metaneutrons/Amiga1200-Plus/Firmware/Keyboard/KeyboardController/KeyboardController/src/driver_init.c

/**
 * \file
 *
 * \brief Driver initialization.
 *
 (c) 2018 Microchip Technology Inc. and its subsidiaries.

    Subject to your compliance with these terms,you may use this software and
    any derivatives exclusively with Microchip products.It is your responsibility
    to comply with third party license terms applicable to your use of third party
    software (including open source software) that may accompany Microchip software.

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
    IN NO EVENT WILL MICROCHIP BE LIABLE FOR ANY INDIRECT, SPECIAL, PUNITIVE,
    INCIDENTAL OR CONSEQUENTIAL LOSS, DAMAGE, COST OR EXPENSE OF ANY KIND
    WHATSOEVER RELATED TO THE SOFTWARE, HOWEVER CAUSED, EVEN IF MICROCHIP HAS
    BEEN ADVISED OF THE POSSIBILITY OR THE DAMAGES ARE FORESEEABLE. TO THE
    FULLEST EXTENT ALLOWED BY LAW, MICROCHIP'S TOTAL LIABILITY ON ALL CLAIMS IN
    ANY WAY RELATED TO THIS SOFTWARE WILL NOT EXCEED THE AMOUNT OF FEES, IF ANY,
    THAT YOU HAVE PAID DIRECTLY TO MICROCHIP FOR THIS SOFTWARE.
 *
 */

/*
 * Code generated by START.
 *
 * This file will be overwritten when reconfiguring your START project.
 * Please copy examples or other code you want to keep to a separate file
 * to avoid losing it when reconfiguring.
 */

#include "driver_init.h"
#include <system.h>

/**
 * \brief System initialization
 */
void system_init()
{
	mcu_init();

	/* PORT setting on PA0 */

	// Set pin direction to input
	Y8_set_dir(PORT_DIR_IN);

	Y8_set_pull_mode(
	    // <y> Pull configuration
	    // <id> pad_pull_config
	    // <PORT_PULL_OFF"> Off
	    // <PORT_PULL_UP"> Pull-up
	    PORT_PULL_UP);

	/* PORT setting on PA1 */

	// Set pin direction to input
	Y9_set_dir(PORT_DIR_IN);

	Y9_set_pull_mode(
	    // <y> Pull configuration
	    // <id> pad_pull_config
	    // <PORT_PULL_OFF"> Off
	    // <PORT_PULL_UP"> Pull-up
	    PORT_PULL_UP);

	/* PORT setting on PA2 */

	// Set pin direction to input
	Y10_set_dir(PORT_DIR_IN);

	Y10_set_pull_mode(
	    // <y> Pull configuration
	    // <id> pad_pull_config
	    // <PORT_PULL_OFF"> Off
	    // <PORT_PULL_UP"> Pull-up
	    PORT_PULL_UP);

	/* PORT setting on PA3 */

	// Set pin direction to input
	Y11_set_dir(PORT_DIR_IN);

	Y11_set_pull_mode(
	    // <y> Pull configuration
	    // <id> pad_pull_config
	    // <PORT_PULL_OFF"> Off
	    // <PORT_PULL_UP"> Pull-up
	    PORT_PULL_UP);

	/* PORT setting on PA4 */

	// Set pin direction to input
	Y12_set_dir(PORT_DIR_IN);

	Y12_set_pull_mode(
	    // <y> Pull configuration
	    // <id> pad_pull_config
	    // <PORT_PULL_OFF"> Off
	    // <PORT_PULL_UP"> Pull-up
	    PORT_PULL_UP);

	/* PORT setting on PA5 */

	// Set pin direction to input
	Y13_set_dir(PORT_DIR_IN);

	Y13_set_pull_mode(
	    // <y> Pull configuration
	    // <id> pad_pull_config
	    // <PORT_PULL_OFF"> Off
	    // <PORT_PULL_UP"> Pull-up
	    PORT_PULL_UP);

	/* PORT setting on PA6 */

	// Set pin direction to input
	Y14_set_dir(PORT_DIR_IN);

	Y14_set_pull_mode(
	    // <y> Pull configuration
	    // <id> pad_pull_config
	    // <PORT_PULL_OFF"> Off
	    // <PORT_PULL_UP"> Pull-up
	    PORT_PULL_UP);

	/* PORT setting on PB0 */

	// Set pin direction to output
	X2_set_dir(PORT_DIR_OUT);

	X2_set_level(
	    // <y> Initial level
	    // <id> pad_initial_level
	    // <false"> Low
	    // <true"> High
	    false);

	/* PORT setting on PB1 */

	// Set pin direction to input
	RALT_set_dir(PORT_DIR_IN);

	RALT_set_pull_mode(
	    // <y> Pull configuration
	    // <id> pad_pull_config
	    // <PORT_PULL_OFF"> Off
	    // <PORT_PULL_UP"> Pull-up
	    PORT_PULL_UP);

	/* PORT setting on PB2 */

	// Set pin direction to input
	RAMI_set_dir(PORT_DIR_IN);

	RAMI_set_pull_mode(
	    // <y> Pull configuration
	    // <id> pad_pull_config
	    // <PORT_PULL_OFF"> Off
	    // <PORT_PULL_UP"> Pull-up
	    PORT_PULL_UP);

	/* PORT setting on PB3 */

	// Set pin direction to input
	CTRL_set_dir(PORT_DIR_IN);

	CTRL_set_pull_mode(
	    // <y> Pull configuration
	    // <id> pad_pull_config
	    // <PORT_PULL_OFF"> Off
	    // <PORT_PULL_UP"> Pull-up
	    PORT_PULL_UP);

	/* PORT setting on PB4 */

	// Set pin direction to input
	LSHF_set_dir(PORT_DIR_IN);

	LSHF_set_pull_mode(
	    // <y> Pull configuration
	    // <id> pad_pull_config
	    // <PORT_PULL_OFF"> Off
	    // <PORT_PULL_UP"> Pull-up
	    PORT_PULL_UP);

	/* PORT setting on PB5 */

	// Set pin direction to input
	LALT_set_dir(PORT_DIR_IN);

	LALT_set_pull_mode(
	    // <y> Pull configuration
	    // <id> pad_pull_config
	    // <PORT_PULL_OFF"> Off
	    // <PORT_PULL_UP"> Pull-up
	    PORT_PULL_UP);

	/* PORT setting on PB6 */

	// Set pin direction to input
	LAMI_set_dir(PORT_DIR_IN);

	LAMI_set_pull_mode(
	    // <y> Pull configuration
	    // <id> pad_pull_config
	    // <PORT_PULL_OFF"> Off
	    // <PORT_PULL_UP"> Pull-up
	    PORT_PULL_UP);

	/* PORT setting on PB7 */

	// Set pin direction to output
	CapsLockLed_set_dir(PORT_DIR_OUT);

	CapsLockLed_set_level(
	    // <y> Initial level
	    // <id> pad_initial_level
	    // <false"> Low
	    // <true"> High
	    false);

	/* PORT setting on PC0 */

	// Set pin direction to input
	Y0_set_dir(PORT_DIR_IN);

	Y0_set_pull_mode(
	    // <y> Pull configuration
	    // <id> pad_pull_config
	    // <PORT_PULL_OFF"> Off
	    // <PORT_PULL_UP"> Pull-up
	    PORT_PULL_UP);

	/* PORT setting on PC1 */

	// Set pin direction to input
	Y1_set_dir(PORT_DIR_IN);

	Y1_set_pull_mode(
	    // <y> Pull configuration
	    // <id> pad_pull_config
	    // <PORT_PULL_OFF"> Off
	    // <PORT_PULL_UP"> Pull-up
	    PORT_PULL_UP);

	/* PORT setting on PC2 */

	// Set pin direction to input
	Y2_set_dir(PORT_DIR_IN);

	Y2_set_pull_mode(
	    // <y> Pull configuration
	    // <id> pad_pull_config
	    // <PORT_PULL_OFF"> Off
	    // <PORT_PULL_UP"> Pull-up
	    PORT_PULL_UP);

	/* PORT setting on PC3 */

	// Set pin direction to input
	Y3_set_dir(PORT_DIR_IN);

	Y3_set_pull_mode(
	    // <y> Pull configuration
	    // <id> pad_pull_config
	    // <PORT_PULL_OFF"> Off
	    // <PORT_PULL_UP"> Pull-up
	    PORT_PULL_UP);

	/* PORT setting on PC4 */

	// Set pin direction to input
	Y4_set_dir(PORT_DIR_IN);

	Y4_set_pull_mode(
	    // <y> Pull configuration
	    // <id> pad_pull_config
	    // <PORT_PULL_OFF"> Off
	    // <PORT_PULL_UP"> Pull-up
	    PORT_PULL_UP);

	/* PORT setting on PC5 */

	// Set pin direction to input
	Y5_set_dir(PORT_DIR_IN);

	Y5_set_pull_mode(
	    // <y> Pull configuration
	    // <id> pad_pull_config
	    // <PORT_PULL_OFF"> Off
	    // <PORT_PULL_UP"> Pull-up
	    PORT_PULL_UP);

	/* PORT setting on PC6 */

	// Set pin direction to input
	Y6_set_dir(PORT_DIR_IN);

	Y6_set_pull_mode(
	    // <y> Pull configuration
	    // <id> pad_pull_config
	    // <PORT_PULL_OFF"> Off
	    // <PORT_PULL_UP"> Pull-up
	    PORT_PULL_UP);

	/* PORT setting on PC7 */

	// Set pin direction to input
	Y7_set_dir(PORT_DIR_IN);

	Y7_set_pull_mode(
	    // <y> Pull configuration
	    // <id> pad_pull_config
	    // <PORT_PULL_OFF"> Off
	    // <PORT_PULL_UP"> Pull-up
	    PORT_PULL_UP);

	/* PORT setting on PD0 */

	// Set pin direction to output
	KB_CLOCK_set_dir(PORT_DIR_OUT);

	KB_CLOCK_set_level(
	    // <y> Initial level
	    // <id> pad_initial_level
	    // <false"> Low
	    // <true"> High
	    false);

	/* PORT setting on PD1 */

	// Set pin direction to output
	KB_DATA_set_dir(PORT_DIR_OUT);

	KB_DATA_set_level(
	    // <y> Initial level
	    // <id> pad_initial_level
	    // <false"> Low
	    // <true"> High
	    false);

	/* PORT setting on PD2 */

	// Set pin direction to input
	KB_DATA_IN_set_dir(PORT_DIR_IN);

	KB_DATA_IN_set_pull_mode(
	    // <y> Pull configuration
	    // <id> pad_pull_config
	    // <PORT_PULL_OFF"> Off
	    // <PORT_PULL_UP"> Pull-up
	    PORT_PULL_OFF);

	/* PORT setting on PD3 */

	// Set pin direction to output
	KB_RESET_set_dir(PORT_DIR_OUT);

	KB_RESET_set_level(
	    // <y> Initial level
	    // <id> pad_initial_level
	    // <false"> Low
	    // <true"> High
	    false);

	/* PORT setting on PD4 */

	// Set pin direction to input
	KB_RESET_INPUT_set_dir(PORT_DIR_IN);

	KB_RESET_INPUT_set_pull_mode(
	    // <y> Pull configuration
	    // <id> pad_pull_config
	    // <PORT_PULL_OFF"> Off
	    // <PORT_PULL_UP"> Pull-up
	    PORT_PULL_OFF);

	/* PORT setting on PE2 */

	// Set pin direction to output
	__BootFromDF0___set_dir(PORT_DIR_OUT);

	__BootFromDF0___set_level(
	    // <y> Initial level
	    // <id> pad_initial_level
	    // <false"> Low
	    // <true"> High
	    false);

	/* PORT setting on PE3 */

	// Set pin direction to output
	__BootFromROM0___set_dir(PORT_DIR_OUT);

	__BootFromROM0___set_level(
	    // <y> Initial level
	    // <id> pad_initial_level
	    // <false"> Low
	    // <true"> High
	    false);

	/* PORT setting on PE4 */

	/* PORT setting on PE5 */

	/* PORT setting on PF0 */

	// Set pin direction to input
	RSHF_set_dir(PORT_DIR_IN);

	RSHF_set_pull_mode(
	    // <y> Pull configuration
	    // <id> pad_pull_config
	    // <PORT_PULL_OFF"> Off
	    // <PORT_PULL_UP"> Pull-up
	    PORT_PULL_UP);

	/* PORT setting on PF1 */

	// Set pin direction to output
	X3_set_dir(PORT_DIR_OUT);

	X3_set_level(
	    // <y> Initial level
	    // <id> pad_initial_level
	    // <false"> Low
	    // <true"> High
	    false);

	/* PORT setting on PF2 */

	// Set pin direction to output
	X4_set_dir(PORT_DIR_OUT);

	X4_set_level(
	    // <y> Initial level
	    // <id> pad_initial_level
	    // <false"> Low
	    // <true"> High
	    false);

	/* PORT setting on PF3 */

	// Set pin direction to output
	X5_set_dir(PORT_DIR_OUT);

	X5_set_level(
	    // <y> Initial level
	    // <id> pad_initial_level
	    // <false"> Low
	    // <true"> High
	    false);

	/* PORT setting on PF4 */

	// Set pin direction to output
	X6_set_dir(PORT_DIR_OUT);

	X6_set_level(
	    // <y> Initial level
	    // <id> pad_initial_level
	    // <false"> Low
	    // <true"> High
	    false);

	/* PORT setting on PF5 */

	// Set pin direction to output
	X7_set_dir(PORT_DIR_OUT);

	X7_set_level(
	    // <y> Initial level
	    // <id> pad_initial_level
	    // <false"> Low
	    // <true"> High
	    false);

	sysctrl_init();
}
