metaneutrons/Amiga1200-Plus/Firmware/Keyboard/KeyboardController/KeyboardController/include/atmel_start_pins.h

/*
 * Code generated from Atmel Start.
 *
 * This file will be overwritten when reconfiguring your Atmel Start project.
 * Please copy examples or other code you want to keep to a separate file
 * to avoid losing it when reconfiguring.
 */
#ifndef ATMEL_START_PINS_H_INCLUDED
#define ATMEL_START_PINS_H_INCLUDED

#include <port.h>

/**
 * \brief Set Y8 pull mode
 *
 * Configure pin to pull up, down or disable pull mode, supported pull
 * modes are defined by device used
 *
 * \param[in] pull_mode Pin pull mode
 */
static inline void Y8_set_pull_mode(const enum port_pull_mode pull_mode)
{
	PORTA_set_pin_pull_mode(0, pull_mode);
}

/**
 * \brief Set Y8 data direction
 *
 * Select if the pin data direction is input, output or disabled.
 * If disabled state is not possible, this function throws an assert.
 *
 * \param[in] direction PORT_DIR_IN  = Data direction in
 *                      PORT_DIR_OUT = Data direction out
 *                      PORT_DIR_OFF = Disables the pin
 *                      (low power state)
 */
static inline void Y8_set_dir(const enum port_dir dir)
{
	PORTA_set_pin_dir(0, dir);
}

/**
 * \brief Set Y8 level
 *
 * Sets output level on a pin
 *
 * \param[in] level true  = Pin level set to "high" state
 *                  false = Pin level set to "low" state
 */
static inline void Y8_set_level(const bool level)
{
	PORTA_set_pin_level(0, level);
}

/**
 * \brief Toggle output level on Y8
 *
 * Toggle the pin level
 */
static inline void Y8_toggle_level()
{
	PORTA_toggle_pin_level(0);
}

/**
 * \brief Get level on Y8
 *
 * Reads the level on a pin
 */
static inline bool Y8_get_level()
{
	return PORTA_get_pin_level(0);
}

/**
 * \brief Set Y9 pull mode
 *
 * Configure pin to pull up, down or disable pull mode, supported pull
 * modes are defined by device used
 *
 * \param[in] pull_mode Pin pull mode
 */
static inline void Y9_set_pull_mode(const enum port_pull_mode pull_mode)
{
	PORTA_set_pin_pull_mode(1, pull_mode);
}

/**
 * \brief Set Y9 data direction
 *
 * Select if the pin data direction is input, output or disabled.
 * If disabled state is not possible, this function throws an assert.
 *
 * \param[in] direction PORT_DIR_IN  = Data direction in
 *                      PORT_DIR_OUT = Data direction out
 *                      PORT_DIR_OFF = Disables the pin
 *                      (low power state)
 */
static inline void Y9_set_dir(const enum port_dir dir)
{
	PORTA_set_pin_dir(1, dir);
}

/**
 * \brief Set Y9 level
 *
 * Sets output level on a pin
 *
 * \param[in] level true  = Pin level set to "high" state
 *                  false = Pin level set to "low" state
 */
static inline void Y9_set_level(const bool level)
{
	PORTA_set_pin_level(1, level);
}

/**
 * \brief Toggle output level on Y9
 *
 * Toggle the pin level
 */
static inline void Y9_toggle_level()
{
	PORTA_toggle_pin_level(1);
}

/**
 * \brief Get level on Y9
 *
 * Reads the level on a pin
 */
static inline bool Y9_get_level()
{
	return PORTA_get_pin_level(1);
}

/**
 * \brief Set Y10 pull mode
 *
 * Configure pin to pull up, down or disable pull mode, supported pull
 * modes are defined by device used
 *
 * \param[in] pull_mode Pin pull mode
 */
static inline void Y10_set_pull_mode(const enum port_pull_mode pull_mode)
{
	PORTA_set_pin_pull_mode(2, pull_mode);
}

/**
 * \brief Set Y10 data direction
 *
 * Select if the pin data direction is input, output or disabled.
 * If disabled state is not possible, this function throws an assert.
 *
 * \param[in] direction PORT_DIR_IN  = Data direction in
 *                      PORT_DIR_OUT = Data direction out
 *                      PORT_DIR_OFF = Disables the pin
 *                      (low power state)
 */
static inline void Y10_set_dir(const enum port_dir dir)
{
	PORTA_set_pin_dir(2, dir);
}

/**
 * \brief Set Y10 level
 *
 * Sets output level on a pin
 *
 * \param[in] level true  = Pin level set to "high" state
 *                  false = Pin level set to "low" state
 */
static inline void Y10_set_level(const bool level)
{
	PORTA_set_pin_level(2, level);
}

/**
 * \brief Toggle output level on Y10
 *
 * Toggle the pin level
 */
static inline void Y10_toggle_level()
{
	PORTA_toggle_pin_level(2);
}

/**
 * \brief Get level on Y10
 *
 * Reads the level on a pin
 */
static inline bool Y10_get_level()
{
	return PORTA_get_pin_level(2);
}

/**
 * \brief Set Y11 pull mode
 *
 * Configure pin to pull up, down or disable pull mode, supported pull
 * modes are defined by device used
 *
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
 *
 * Configure pin to pull up, down or disable pull mode, supported pull
 * modes are defined by device used
 *
 * \param[in] pull_mode Pin pull mode
 */
static inline void Y14_set_pull_mode(const enum port_pull_mode pull_mode)
{
	PORTA_set_pin_pull_mode(6, pull_mode);
}

/**
 * \brief Set Y14 data direction
 *
 * Select if the pin data direction is input, output or disabled.
 * If disabled state is not possible, this function throws an assert.
 *
 * \param[in] direction PORT_DIR_IN  = Data direction in
 *                      PORT_DIR_OUT = Data direction out
 *                      PORT_DIR_OFF = Disables the pin
 *                      (low power state)
 */
static inline void Y14_set_dir(const enum port_dir dir)
{
	PORTA_set_pin_dir(6, dir);
}

/**
 * \brief Set Y14 level
 *
 * Sets output level on a pin
 *
 * \param[in] level true  = Pin level set to "high" state
 *                  false = Pin level set to "low" state
 */
static inline void Y14_set_level(const bool level)
{
	PORTA_set_pin_level(6, level);
}

/**
 * \brief Toggle output level on Y14
 *
 * Toggle the pin level
 */
static inline void Y14_toggle_level()
{
	PORTA_toggle_pin_level(6);
}

/**
 * \brief Get level on Y14
 *
 * Reads the level on a pin
 */
static inline bool Y14_get_level()
{
	return PORTA_get_pin_level(6);
}

/**
 * \brief Set X2 pull mode
 *
 * Configure pin to pull up, down or disable pull mode, supported pull
 * modes are defined by device used
 *
 * \param[in] pull_mode Pin pull mode
 */
static inline void X2_set_pull_mode(const enum port_pull_mode pull_mode)
{
	PORTB_set_pin_pull_mode(0, pull_mode);
}

/**
 * \brief Set X2 data direction
 *
 * Select if the pin data direction is input, output or disabled.
 * If disabled state is not possible, this function throws an assert.
 *
 * \param[in] direction PORT_DIR_IN  = Data direction in
 *                      PORT_DIR_OUT = Data direction out
 *                      PORT_DIR_OFF = Disables the pin
 *                      (low power state)
 */
static inline void X2_set_dir(const enum port_dir dir)
{
	PORTB_set_pin_dir(0, dir);
}

/**
 * \brief Set X2 level
 *
 * Sets output level on a pin
 *
 * \param[in] level true  = Pin level set to "high" state
 *                  false = Pin level set to "low" state
 */
static inline void X2_set_level(const bool level)
{
	PORTB_set_pin_level(0, level);
}

/**
 * \brief Toggle output level on X2
 *
 * Toggle the pin level
 */
static inline void X2_toggle_level()
{
	PORTB_toggle_pin_level(0);
}

/**
 * \brief Get level on X2
 *
 * Reads the level on a pin
 */
static inline bool X2_get_level()
{
	return PORTB_get_pin_level(0);
}

/**
 * \brief Set RALT pull mode
 *
 * Configure pin to pull up, down or disable pull mode, supported pull
 * modes are defined by device used
 *
 * \param[in] pull_mode Pin pull mode
 */
static inline void RALT_set_pull_mode(const enum port_pull_mode pull_mode)
{
	PORTB_set_pin_pull_mode(1, pull_mode);
}

/**
 * \brief Set RALT data direction
 *
 * Select if the pin data direction is input, output or disabled.
 * If disabled state is not possible, this function throws an assert.
 *
 * \param[in] direction PORT_DIR_IN  = Data direction in
 *                      PORT_DIR_OUT = Data direction out
 *                      PORT_DIR_OFF = Disables the pin
 *                      (low power state)
 */
static inline void RALT_set_dir(const enum port_dir dir)
{
	PORTB_set_pin_dir(1, dir);
}

/**
 * \brief Set RALT level
 *
 * Sets output level on a pin
 *
 * \param[in] level true  = Pin level set to "high" state
 *                  false = Pin level set to "low" state
 */
static inline void RALT_set_level(const bool level)
{
	PORTB_set_pin_level(1, level);
}

/**
 * \brief Toggle output level on RALT
 *
 * Toggle the pin level
 */
static inline void RALT_toggle_level()
{
	PORTB_toggle_pin_level(1);
}

/**
 * \brief Get level on RALT
 *
 * Reads the level on a pin
 */
static inline bool RALT_get_level()
{
	return PORTB_get_pin_level(1);
}

/**
 * \brief Set RAMI pull mode
 *
 * Configure pin to pull up, down or disable pull mode, supported pull
 * modes are defined by device used
 *
 * \param[in] pull_mode Pin pull mode
 */
static inline void RAMI_set_pull_mode(const enum port_pull_mode pull_mode)
{
	PORTB_set_pin_pull_mode(2, pull_mode);
}

/**
 * \brief Set RAMI data direction
 *
 * Select if the pin data direction is input, output or disabled.
 * If disabled state is not possible, this function throws an assert.
 *
 * \param[in] direction PORT_DIR_IN  = Data direction in
 *                      PORT_DIR_OUT = Data direction out
 *                      PORT_DIR_OFF = Disables the pin
 *                      (low power state)
 */
static inline void RAMI_set_dir(const enum port_dir dir)
{
	PORTB_set_pin_dir(2, dir);
}

/**
 * \brief Set RAMI level
 *
 * Sets output level on a pin
 *
 * \param[in] level true  = Pin level set to "high" state
 *                  false = Pin level set to "low" state
 */
static inline void RAMI_set_level(const bool level)
{
	PORTB_set_pin_level(2, level);
}

/**
 * \brief Toggle output level on RAMI
 *
 * Toggle the pin level
 */
static inline void RAMI_toggle_level()
{
	PORTB_toggle_pin_level(2);
}

/**
 * \brief Get level on RAMI
 *
 * Reads the level on a pin
 */
static inline bool RAMI_get_level()
{
	return PORTB_get_pin_level(2);
}

/**
 * \brief Set CTRL pull mode
 *
 * Configure pin to pull up, down or disable pull mode, supported pull
 * modes are defined by device used
 *
 * \param[in] pull_mode Pin pull mode
 */
static inline void CTRL_set_pull_mode(const enum port_pull_mode pull_mode)
{
	PORTB_set_pin_pull_mode(3, pull_mode);
}

/**
 * \brief Set CTRL data direction
 *
 * Select if the pin data direction is input, output or disabled.
 * If disabled state is not possible, this function throws an assert.
 *
 * \param[in] direction PORT_DIR_IN  = Data direction in
 *                      PORT_DIR_OUT = Data direction out
 *                      PORT_DIR_OFF = Disables the pin
 *                      (low power state)
 */
static inline void CTRL_set_dir(const enum port_dir dir)
{
	PORTB_set_pin_dir(3, dir);
}

/**
 * \brief Set CTRL level
 *
 * Sets output level on a pin
 *
 * \param[in] level true  = Pin level set to "high" state
 *                  false = Pin level set to "low" state
 */
static inline void CTRL_set_level(const bool level)
{
	PORTB_set_pin_level(3, level);
}

/**
 * \brief Toggle output level on CTRL
 *
 * Toggle the pin level
 */
static inline void CTRL_toggle_level()
{
	PORTB_toggle_pin_level(3);
}

/**
 * \brief Get level on CTRL
 *
 * Reads the level on a pin
 */
static inline bool CTRL_get_level()
{
	return PORTB_get_pin_level(3);
}

/**
 * \brief Set LSHF pull mode
 *
 * Configure pin to pull up, down or disable pull mode, supported pull
 * modes are defined by device used
 *
 * \param[in] pull_mode Pin pull mode
 */
static inline void LSHF_set_pull_mode(const enum port_pull_mode pull_mode)
{
	PORTB_set_pin_pull_mode(4, pull_mode);
}

/**
 * \brief Set LSHF data direction
 *
 * Select if the pin data direction is input, output or disabled.
 * If disabled state is not possible, this function throws an assert.
 *
 * \param[in] direction PORT_DIR_IN  = Data direction in
 *                      PORT_DIR_OUT = Data direction out
 *                      PORT_DIR_OFF = Disables the pin
 *                      (low power state)
 */
static inline void LSHF_set_dir(const enum port_dir dir)
{
	PORTB_set_pin_dir(4, dir);
}

/**
 * \brief Set LSHF level
 *
 * Sets output level on a pin
 *
 * \param[in] level true  = Pin level set to "high" state
 *                  false = Pin level set to "low" state
 */
static inline void LSHF_set_level(const bool level)
{
	PORTB_set_pin_level(4, level);
}

/**
 * \brief Toggle output level on LSHF
 *
 * Toggle the pin level
 */
static inline void LSHF_toggle_level()
{
	PORTB_toggle_pin_level(4);
}

/**
 * \brief Get level on LSHF
 *
 * Reads the level on a pin
 */
static inline bool LSHF_get_level()
{
	return PORTB_get_pin_level(4);
}

/**
 * \brief Set LALT pull mode
 *
 * Configure pin to pull up, down or disable pull mode, supported pull
 * modes are defined by device used
 *
 * \param[in] pull_mode Pin pull mode
 */
static inline void LALT_set_pull_mode(const enum port_pull_mode pull_mode)
{
	PORTB_set_pin_pull_mode(5, pull_mode);
}

/**
 * \brief Set LALT data direction
 *
 * Select if the pin data direction is input, output or disabled.
 * If disabled state is not possible, this function throws an assert.
 *
 * \param[in] direction PORT_DIR_IN  = Data direction in
 *                      PORT_DIR_OUT = Data direction out
 *                      PORT_DIR_OFF = Disables the pin
 *                      (low power state)
 */
static inline void LALT_set_dir(const enum port_dir dir)
{
	PORTB_set_pin_dir(5, dir);
}

/**
 * \brief Set LALT level
 *
 * Sets output level on a pin
 *
 * \param[in] level true  = Pin level set to "high" state
 *                  false = Pin level set to "low" state
 */
static inline void LALT_set_level(const bool level)
{
	PORTB_set_pin_level(5, level);
}

/**
 * \brief Toggle output level on LALT
 *
 * Toggle the pin level
 */
static inline void LALT_toggle_level()
{
	PORTB_toggle_pin_level(5);
}

/**
 * \brief Get level on LALT
 *
 * Reads the level on a pin
 */
static inline bool LALT_get_level()
{
	return PORTB_get_pin_level(5);
}

/**
 * \brief Set LAMI pull mode
 *
 * Configure pin to pull up, down or disable pull mode, supported pull
 * modes are defined by device used
 *
 * \param[in] pull_mode Pin pull mode
 */
static inline void LAMI_set_pull_mode(const enum port_pull_mode pull_mode)
{
	PORTB_set_pin_pull_mode(6, pull_mode);
}

/**
 * \brief Set LAMI data direction
 *
 * Select if the pin data direction is input, output or disabled.
 * If disabled state is not possible, this function throws an assert.
 *
 * \param[in] direction PORT_DIR_IN  = Data direction in
 *                      PORT_DIR_OUT = Data direction out
 *                      PORT_DIR_OFF = Disables the pin
 *                      (low power state)
 */
static inline void LAMI_set_dir(const enum port_dir dir)
{
	PORTB_set_pin_dir(6, dir);
}

/**
 * \brief Set LAMI level
 *
 * Sets output level on a pin
 *
 * \param[in] level true  = Pin level set to "high" state
 *                  false = Pin level set to "low" state
 */
static inline void LAMI_set_level(const bool level)
{
	PORTB_set_pin_level(6, level);
}

/**
 * \brief Toggle output level on LAMI
 *
 * Toggle the pin level
 */
static inline void LAMI_toggle_level()
{
	PORTB_toggle_pin_level(6);
}

/**
 * \brief Get level on LAMI
 *
 * Reads the level on a pin
 */
static inline bool LAMI_get_level()
{
	return PORTB_get_pin_level(6);
}

/**
 * \brief Set CapsLockLed pull mode
 *
 * Configure pin to pull up, down or disable pull mode, supported pull
 * modes are defined by device used
 *
 * \param[in] pull_mode Pin pull mode
 */
static inline void CapsLockLed_set_pull_mode(const enum port_pull_mode pull_mode)
{
	PORTB_set_pin_pull_mode(7, pull_mode);
}

/**
 * \brief Set CapsLockLed data direction
 *
 * Select if the pin data direction is input, output or disabled.
 * If disabled state is not possible, this function throws an assert.
 *
 * \param[in] direction PORT_DIR_IN  = Data direction in
 *                      PORT_DIR_OUT = Data direction out
 *                      PORT_DIR_OFF = Disables the pin
 *                      (low power state)
 */
static inline void CapsLockLed_set_dir(const enum port_dir dir)
{
	PORTB_set_pin_dir(7, dir);
}

/**
 * \brief Set CapsLockLed level
 *
 * Sets output level on a pin
 *
 * \param[in] level true  = Pin level set to "high" state
 *                  false = Pin level set to "low" state
 */
static inline void CapsLockLed_set_level(const bool level)
{
	PORTB_set_pin_level(7, level);
}

/**
 * \brief Toggle output level on CapsLockLed
 *
 * Toggle the pin level
 */
static inline void CapsLockLed_toggle_level()
{
	PORTB_toggle_pin_level(7);
}

/**
 * \brief Get level on CapsLockLed
 *
 * Reads the level on a pin
 */
static inline bool CapsLockLed_get_level()
{
	return PORTB_get_pin_level(7);
}

/**
 * \brief Set Y0 pull mode
 *
 * Configure pin to pull up, down or disable pull mode, supported pull
 * modes are defined by device used
 *
 * \param[in] pull_mode Pin pull mode
 */
static inline void Y0_set_pull_mode(const enum port_pull_mode pull_mode)
{
	PORTC_set_pin_pull_mode(0, pull_mode);
}

/**
 * \brief Set Y0 data direction
 *
 * Select if the pin data direction is input, output or disabled.
 * If disabled state is not possible, this function throws an assert.
 *
 * \param[in] direction PORT_DIR_IN  = Data direction in
 *                      PORT_DIR_OUT = Data direction out
 *                      PORT_DIR_OFF = Disables the pin
 *                      (low power state)
 */
static inline void Y0_set_dir(const enum port_dir dir)
{
	PORTC_set_pin_dir(0, dir);
}

/**
 * \brief Set Y0 level
 *
 * Sets output level on a pin
 *
 * \param[in] level true  = Pin level set to "high" state
 *                  false = Pin level set to "low" state
 */
static inline void Y0_set_level(const bool level)
{
	PORTC_set_pin_level(0, level);
}

/**
 * \brief Toggle output level on Y0
 *
 * Toggle the pin level
 */
static inline void Y0_toggle_level()
{
	PORTC_toggle_pin_level(0);
}

/**
 * \brief Get level on Y0
 *
 * Reads the level on a pin
 */
static inline bool Y0_get_level()
{
	return PORTC_get_pin_level(0);
}

/**
 * \brief Set Y1 pull mode
 *
 * Configure pin to pull up, down or disable pull mode, supported pull
 * modes are defined by device used
 *
 * \param[in] pull_mode Pin pull mode
 */
static inline void Y1_set_pull_mode(const enum port_pull_mode pull_mode)
{
	PORTC_set_pin_pull_mode(1, pull_mode);
}

/**
 * \brief Set Y1 data direction
 *
 * Select if the pin data direction is input, output or disabled.
 * If disabled state is not possible, this function throws an assert.
 *
 * \param[in] direction PORT_DIR_IN  = Data direction in
 *                      PORT_DIR_OUT = Data direction out
 *                      PORT_DIR_OFF = Disables the pin
 *                      (low power state)
 */
static inline void Y1_set_dir(const enum port_dir dir)
{
	PORTC_set_pin_dir(1, dir);
}

/**
 * \brief Set Y1 level
 *
 * Sets output level on a pin
 *
 * \param[in] level true  = Pin level set to "high" state
 *                  false = Pin level set to "low" state
 */
static inline void Y1_set_level(const bool level)
{
	PORTC_set_pin_level(1, level);
}

/**
 * \brief Toggle output level on Y1
 *
 * Toggle the pin level
 */
static inline void Y1_toggle_level()
{
	PORTC_toggle_pin_level(1);
}

/**
 * \brief Get level on Y1
 *
 * Reads the level on a pin
 */
static inline bool Y1_get_level()
{
	return PORTC_get_pin_level(1);
}

/**
 * \brief Set Y2 pull mode
 *
 * Configure pin to pull up, down or disable pull mode, supported pull
 * modes are defined by device used
 *
 * \param[in] pull_mode Pin pull mode
 */
static inline void Y2_set_pull_mode(const enum port_pull_mode pull_mode)
{
	PORTC_set_pin_pull_mode(2, pull_mode);
}

/**
 * \brief Set Y2 data direction
 *
 * Select if the pin data direction is input, output or disabled.
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
 *
 * Configure pin to pull up, down or disable pull mode, supported pull
 * modes are defined by device used
 *
 * \param[in] pull_mode Pin pull mode
 */
static inline void Y7_set_pull_mode(const enum port_pull_mode pull_mode)
{
	PORTC_set_pin_pull_mode(7, pull_mode);
}

/**
 * \brief Set Y7 data direction
 *
 * Select if the pin data direction is input, output or disabled.
 * If disabled state is not possible, this function throws an assert.
 *
 * \param[in] direction PORT_DIR_IN  = Data direction in
 *                      PORT_DIR_OUT = Data direction out
 *                      PORT_DIR_OFF = Disables the pin
 *                      (low power state)
 */
static inline void Y7_set_dir(const enum port_dir dir)
{
	PORTC_set_pin_dir(7, dir);
}

/**
 * \brief Set Y7 level
 *
 * Sets output level on a pin
 *
 * \param[in] level true  = Pin level set to "high" state
 *                  false = Pin level set to "low" state
 */
static inline void Y7_set_level(const bool level)
{
	PORTC_set_pin_level(7, level);
}

/**
 * \brief Toggle output level on Y7
 *
 * Toggle the pin level
 */
static inline void Y7_toggle_level()
{
	PORTC_toggle_pin_level(7);
}

/**
 * \brief Get level on Y7
 *
 * Reads the level on a pin
 */
static inline bool Y7_get_level()
{
	return PORTC_get_pin_level(7);
}

/**
 * \brief Set KB_CLOCK pull mode
 *
 * Configure pin to pull up, down or disable pull mode, supported pull
 * modes are defined by device used
 *
 * \param[in] pull_mode Pin pull mode
 */
static inline void KB_CLOCK_set_pull_mode(const enum port_pull_mode pull_mode)
{
	PORTD_set_pin_pull_mode(0, pull_mode);
}

/**
 * \brief Set KB_CLOCK data direction
 *
 * Select if the pin data direction is input, output or disabled.
 * If disabled state is not possible, this function throws an assert.
 *
 * \param[in] direction PORT_DIR_IN  = Data direction in
 *                      PORT_DIR_OUT = Data direction out
 *                      PORT_DIR_OFF = Disables the pin
 *                      (low power state)
 */
static inline void KB_CLOCK_set_dir(const enum port_dir dir)
{
	PORTD_set_pin_dir(0, dir);
}

/**
 * \brief Set KB_CLOCK level
 *
 * Sets output level on a pin
 *
 * \param[in] level true  = Pin level set to "high" state
 *                  false = Pin level set to "low" state
 */
static inline void KB_CLOCK_set_level(const bool level)
{
	PORTD_set_pin_level(0, level);
}

/**
 * \brief Toggle output level on KB_CLOCK
 *
 * Toggle the pin level
 */
static inline void KB_CLOCK_toggle_level()
{
	PORTD_toggle_pin_level(0);
}

/**
 * \brief Get level on KB_CLOCK
 *
 * Reads the level on a pin
 */
static inline bool KB_CLOCK_get_level()
{
	return PORTD_get_pin_level(0);
}

/**
 * \brief Set KB_DATA pull mode
 *
 * Configure pin to pull up, down or disable pull mode, supported pull
 * modes are defined by device used
 *
 * \param[in] pull_mode Pin pull mode
 */
static inline void KB_DATA_set_pull_mode(const enum port_pull_mode pull_mode)
{
	PORTD_set_pin_pull_mode(1, pull_mode);
}

/**
 * \brief Set KB_DATA data direction
 *
 * Select if the pin data direction is input, output or disabled.
 * If disabled state is not possible, this function throws an assert.
 *
 * \param[in] direction PORT_DIR_IN  = Data direction in
 *                      PORT_DIR_OUT = Data direction out
 *                      PORT_DIR_OFF = Disables the pin
 *                      (low power state)
 */
static inline void KB_DATA_set_dir(const enum port_dir dir)
{
	PORTD_set_pin_dir(1, dir);
}

/**
 * \brief Set KB_DATA level
 *
 * Sets output level on a pin
 *
 * \param[in] level true  = Pin level set to "high" state
 *                  false = Pin level set to "low" state
 */
static inline void KB_DATA_set_level(const bool level)
{
	PORTD_set_pin_level(1, level);
}

/**
 * \brief Toggle output level on KB_DATA
 *
 * Toggle the pin level
 */
static inline void KB_DATA_toggle_level()
{
	PORTD_toggle_pin_level(1);
}

/**
 * \brief Get level on KB_DATA
 *
 * Reads the level on a pin
 */
static inline bool KB_DATA_get_level()
{
	return PORTD_get_pin_level(1);
}

/**
 * \brief Set KB_DATA_IN pull mode
 *
 * Configure pin to pull up, down or disable pull mode, supported pull
 * modes are defined by device used
 *
 * \param[in] pull_mode Pin pull mode
 */
static inline void KB_DATA_IN_set_pull_mode(const enum port_pull_mode pull_mode)
{
	PORTD_set_pin_pull_mode(2, pull_mode);
}

/**
 * \brief Set KB_DATA_IN data direction
 *
 * Select if the pin data direction is input, output or disabled.
 * If disabled state is not possible, this function throws an assert.
 *
 * \param[in] direction PORT_DIR_IN  = Data direction in
 *                      PORT_DIR_OUT = Data direction out
 *                      PORT_DIR_OFF = Disables the pin
 *                      (low power state)
 */
static inline void KB_DATA_IN_set_dir(const enum port_dir dir)
{
	PORTD_set_pin_dir(2, dir);
}

/**
 * \brief Set KB_DATA_IN level
 *
 * Sets output level on a pin
 *
 * \param[in] level true  = Pin level set to "high" state
 *                  false = Pin level set to "low" state
 */
static inline void KB_DATA_IN_set_level(const bool level)
{
	PORTD_set_pin_level(2, level);
}

/**
 * \brief Toggle output level on KB_DATA_IN
 *
 * Toggle the pin level
 */
static inline void KB_DATA_IN_toggle_level()
{
	PORTD_toggle_pin_level(2);
}

/**
 * \brief Get level on KB_DATA_IN
 *
 * Reads the level on a pin
 */
static inline bool KB_DATA_IN_get_level()
{
	return PORTD_get_pin_level(2);
}

/**
 * \brief Set KB_RESET pull mode
 *
 * Configure pin to pull up, down or disable pull mode, supported pull
 * modes are defined by device used
 *
 * \param[in] pull_mode Pin pull mode
 */
static inline void KB_RESET_set_pull_mode(const enum port_pull_mode pull_mode)
{
	PORTD_set_pin_pull_mode(3, pull_mode);
}

/**
 * \brief Set KB_RESET data direction
 *
 * Select if the pin data direction is input, output or disabled.
 * If disabled state is not possible, this function throws an assert.
 *
 * \param[in] direction PORT_DIR_IN  = Data direction in
 *                      PORT_DIR_OUT = Data direction out
 *                      PORT_DIR_OFF = Disables the pin
 *                      (low power state)
 */
static inline void KB_RESET_set_dir(const enum port_dir dir)
{
	PORTD_set_pin_dir(3, dir);
}

/**
 * \brief Set KB_RESET level
 *
 * Sets output level on a pin
 *
 * \param[in] level true  = Pin level set to "high" state
 *                  false = Pin level set to "low" state
 */
static inline void KB_RESET_set_level(const bool level)
{
	PORTD_set_pin_level(3, level);
}

/**
 * \brief Toggle output level on KB_RESET
 *
 * Toggle the pin level
 */
static inline void KB_RESET_toggle_level()
{
	PORTD_toggle_pin_level(3);
}

/**
 * \brief Get level on KB_RESET
 *
 * Reads the level on a pin
 */
static inline bool KB_RESET_get_level()
{
	return PORTD_get_pin_level(3);
}

/**
 * \brief Set KB_RESET_INPUT pull mode
 *
 * Configure pin to pull up, down or disable pull mode, supported pull
 * modes are defined by device used
 *
 * \param[in] pull_mode Pin pull mode
 */
static inline void KB_RESET_INPUT_set_pull_mode(const enum port_pull_mode pull_mode)
{
	PORTD_set_pin_pull_mode(4, pull_mode);
}

/**
 * \brief Set KB_RESET_INPUT data direction
 *
 * Select if the pin data direction is input, output or disabled.
 * If disabled state is not possible, this function throws an assert.
 *
 * \param[in] direction PORT_DIR_IN  = Data direction in
 *                      PORT_DIR_OUT = Data direction out
 *                      PORT_DIR_OFF = Disables the pin
 *                      (low power state)
 */
static inline void KB_RESET_INPUT_set_dir(const enum port_dir dir)
{
	PORTD_set_pin_dir(4, dir);
}

/**
 * \brief Set KB_RESET_INPUT level
 *
 * Sets output level on a pin
 *
 * \param[in] level true  = Pin level set to "high" state
 *                  false = Pin level set to "low" state
 */
static inline void KB_RESET_INPUT_set_level(const bool level)
{
	PORTD_set_pin_level(4, level);
}

/**
 * \brief Toggle output level on KB_RESET_INPUT
 *
 * Toggle the pin level
 */
static inline void KB_RESET_INPUT_toggle_level()
{
	PORTD_toggle_pin_level(4);
}

/**
 * \brief Get level on KB_RESET_INPUT
 *
 * Reads the level on a pin
 */
static inline bool KB_RESET_INPUT_get_level()
{
	return PORTD_get_pin_level(4);
}

/**
 * \brief Set __BootFromDF0__ pull mode
 *
 * Configure pin to pull up, down or disable pull mode, supported pull
 * modes are defined by device used
 *
 * \param[in] pull_mode Pin pull mode
 */
static inline void __BootFromDF0___set_pull_mode(const enum port_pull_mode pull_mode)
{
	PORTE_set_pin_pull_mode(2, pull_mode);
}

/**
 * \brief Set __BootFromDF0__ data direction
 *
 * Select if the pin data direction is input, output or disabled.
 * If disabled state is not possible, this function throws an assert.
 *
 * \param[in] direction PORT_DIR_IN  = Data direction in
 *                      PORT_DIR_OUT = Data direction out
 *                      PORT_DIR_OFF = Disables the pin
 *                      (low power state)
 */
static inline void __BootFromDF0___set_dir(const enum port_dir dir)
{
	PORTE_set_pin_dir(2, dir);
}

/**
 * \brief Set __BootFromDF0__ level
 *
 * Sets output level on a pin
 *
 * \param[in] level true  = Pin level set to "high" state
 *                  false = Pin level set to "low" state
 */
static inline void __BootFromDF0___set_level(const bool level)
{
	PORTE_set_pin_level(2, level);
}

/**
 * \brief Toggle output level on __BootFromDF0__
 *
 * Toggle the pin level
 */
static inline void __BootFromDF0___toggle_level()
{
	PORTE_toggle_pin_level(2);
}

/**
 * \brief Get level on __BootFromDF0__
 *
 * Reads the level on a pin
 */
static inline bool __BootFromDF0___get_level()
{
	return PORTE_get_pin_level(2);
}

/**
 * \brief Set __BootFromROM0__ pull mode
 *
 * Configure pin to pull up, down or disable pull mode, supported pull
 * modes are defined by device used
 *
 * \param[in] pull_mode Pin pull mode
 */
static inline void __BootFromROM0___set_pull_mode(const enum port_pull_mode pull_mode)
{
	PORTE_set_pin_pull_mode(3, pull_mode);
}

/**
 * \brief Set __BootFromROM0__ data direction
 *
 * Select if the pin data direction is input, output or disabled.
 * If disabled state is not possible, this function throws an assert.
 *
 * \param[in] direction PORT_DIR_IN  = Data direction in
 *                      PORT_DIR_OUT = Data direction out
 *                      PORT_DIR_OFF = Disables the pin
 *                      (low power state)
 */
static inline void __BootFromROM0___set_dir(const enum port_dir dir)
{
	PORTE_set_pin_dir(3, dir);
}

/**
 * \brief Set __BootFromROM0__ level
 *
 * Sets output level on a pin
 *
 * \param[in] level true  = Pin level set to "high" state
 *                  false = Pin level set to "low" state
 */
static inline void __BootFromROM0___set_level(const bool level)
{
	PORTE_set_pin_level(3, level);
}

/**
 * \brief Toggle output level on __BootFromROM0__
 *
 * Toggle the pin level
 */
static inline void __BootFromROM0___toggle_level()
{
	PORTE_toggle_pin_level(3);
}

/**
 * \brief Get level on __BootFromROM0__
 *
 * Reads the level on a pin
 */
static inline bool __BootFromROM0___get_level()
{
	return PORTE_get_pin_level(3);
}

/**
 * \brief Set I2C_SCL pull mode
 *
 * Configure pin to pull up, down or disable pull mode, supported pull
 * modes are defined by device used
 *
 * \param[in] pull_mode Pin pull mode
 */
static inline void I2C_SCL_set_pull_mode(const enum port_pull_mode pull_mode)
{
	PORTE_set_pin_pull_mode(4, pull_mode);
}

/**
 * \brief Set I2C_SCL data direction
 *
 * Select if the pin data direction is input, output or disabled.
 * If disabled state is not possible, this function throws an assert.
 *
 * \param[in] direction PORT_DIR_IN  = Data direction in
 *                      PORT_DIR_OUT = Data direction out
 *                      PORT_DIR_OFF = Disables the pin
 *                      (low power state)
 */
static inline void I2C_SCL_set_dir(const enum port_dir dir)
{
	PORTE_set_pin_dir(4, dir);
}

/**
 * \brief Set I2C_SCL level
 *
 * Sets output level on a pin
 *
 * \param[in] level true  = Pin level set to "high" state
 *                  false = Pin level set to "low" state
 */
static inline void I2C_SCL_set_level(const bool level)
{
	PORTE_set_pin_level(4, level);
}

/**
 * \brief Toggle output level on I2C_SCL
 *
 * Toggle the pin level
 */
static inline void I2C_SCL_toggle_level()
{
	PORTE_toggle_pin_level(4);
}

/**
 * \brief Get level on I2C_SCL
 *
 * Reads the level on a pin
 */
static inline bool I2C_SCL_get_level()
{
	return PORTE_get_pin_level(4);
}

/**
 * \brief Set I2C_SDA pull mode
 *
 * Configure pin to pull up, down or disable pull mode, supported pull
 * modes are defined by device used
 *
 * \param[in] pull_mode Pin pull mode
 */
static inline void I2C_SDA_set_pull_mode(const enum port_pull_mode pull_mode)
{
	PORTE_set_pin_pull_mode(5, pull_mode);
}

/**
 * \brief Set I2C_SDA data direction
 *
 * Select if the pin data direction is input, output or disabled.
 * If disabled state is not possible, this function throws an assert.
 *
 * \param[in] direction PORT_DIR_IN  = Data direction in
 *                      PORT_DIR_OUT = Data direction out
 *                      PORT_DIR_OFF = Disables the pin
 *                      (low power state)
 */
static inline void I2C_SDA_set_dir(const enum port_dir dir)
{
	PORTE_set_pin_dir(5, dir);
}

/**
 * \brief Set I2C_SDA level
 *
 * Sets output level on a pin
 *
 * \param[in] level true  = Pin level set to "high" state
 *                  false = Pin level set to "low" state
 */
static inline void I2C_SDA_set_level(const bool level)
{
	PORTE_set_pin_level(5, level);
}

/**
 * \brief Toggle output level on I2C_SDA
 *
 * Toggle the pin level
 */
static inline void I2C_SDA_toggle_level()
{
	PORTE_toggle_pin_level(5);
}

/**
 * \brief Get level on I2C_SDA
 *
 * Reads the level on a pin
 */
static inline bool I2C_SDA_get_level()
{
	return PORTE_get_pin_level(5);
}

/**
 * \brief Set RSHF pull mode
 *
 * Configure pin to pull up, down or disable pull mode, supported pull
 * modes are defined by device used
 *
 * \param[in] pull_mode Pin pull mode
 */
static inline void RSHF_set_pull_mode(const enum port_pull_mode pull_mode)
{
	PORTF_set_pin_pull_mode(0, pull_mode);
}

/**
 * \brief Set RSHF data direction
 *
 * Select if the pin data direction is input, output or disabled.
 * If disabled state is not possible, this function throws an assert.
 *
 * \param[in] direction PORT_DIR_IN  = Data direction in
 *                      PORT_DIR_OUT = Data direction out
 *                      PORT_DIR_OFF = Disables the pin
 *                      (low power state)
 */
static inline void RSHF_set_dir(const enum port_dir dir)
{
	PORTF_set_pin_dir(0, dir);
}

/**
 * \brief Set RSHF level
 *
 * Sets output level on a pin
 *
 * \param[in] level true  = Pin level set to "high" state
 *                  false = Pin level set to "low" state
 */
static inline void RSHF_set_level(const bool level)
{
	PORTF_set_pin_level(0, level);
}

/**
 * \brief Toggle output level on RSHF
 *
 * Toggle the pin level
 */
static inline void RSHF_toggle_level()
{
	PORTF_toggle_pin_level(0);
}

/**
 * \brief Get level on RSHF
 *
 * Reads the level on a pin
 */
static inline bool RSHF_get_level()
{
	return PORTF_get_pin_level(0);
}

/**
 * \brief Set X3 pull mode
 *
 * Configure pin to pull up, down or disable pull mode, supported pull
 * modes are defined by device used
 *
 * \param[in] pull_mode Pin pull mode
 */
static inline void X3_set_pull_mode(const enum port_pull_mode pull_mode)
{
	PORTF_set_pin_pull_mode(1, pull_mode);
}

/**
 * \brief Set X3 data direction
 *
 * Select if the pin data direction is input, output or disabled.
 * If disabled state is not possible, this function throws an assert.
 *
 * \param[in] direction PORT_DIR_IN  = Data direction in
 *                      PORT_DIR_OUT = Data direction out
 *                      PORT_DIR_OFF = Disables the pin
 *                      (low power state)
 */
static inline void X3_set_dir(const enum port_dir dir)
{
	PORTF_set_pin_dir(1, dir);
}

/**
 * \brief Set X3 level
 *
 * Sets output level on a pin
 *
 * \param[in] level true  = Pin level set to "high" state
 *                  false = Pin level set to "low" state
 */
static inline void X3_set_level(const bool level)
{
	PORTF_set_pin_level(1, level);
}

/**
 * \brief Toggle output level on X3
 *
 * Toggle the pin level
 */
static inline void X3_toggle_level()
{
	PORTF_toggle_pin_level(1);
}

/**
 * \brief Get level on X3
 *
 * Reads the level on a pin
 */
static inline bool X3_get_level()
{
	return PORTF_get_pin_level(1);
}

/**
 * \brief Set X4 pull mode
 *
 * Configure pin to pull up, down or disable pull mode, supported pull
 * modes are defined by device used
 *
 * \param[in] pull_mode Pin pull mode
 */
static inline void X4_set_pull_mode(const enum port_pull_mode pull_mode)
{
	PORTF_set_pin_pull_mode(2, pull_mode);
}

/**
 * \brief Set X4 data direction
 *
 * Select if the pin data direction is input, output or disabled.
 * If disabled state is not possible, this function throws an assert.
 *
 * \param[in] direction PORT_DIR_IN  = Data direction in
 *                      PORT_DIR_OUT = Data direction out
 *                      PORT_DIR_OFF = Disables the pin
 *                      (low power state)
 */
static inline void X4_set_dir(const enum port_dir dir)
{
	PORTF_set_pin_dir(2, dir);
}

/**
 * \brief Set X4 level
 *
 * Sets output level on a pin
 *
 * \param[in] level true  = Pin level set to "high" state
 *                  false = Pin level set to "low" state
 */
static inline void X4_set_level(const bool level)
{
	PORTF_set_pin_level(2, level);
}

/**
 * \brief Toggle output level on X4
 *
 * Toggle the pin level
 */
static inline void X4_toggle_level()
{
	PORTF_toggle_pin_level(2);
}

/**
 * \brief Get level on X4
 *
 * Reads the level on a pin
 */
static inline bool X4_get_level()
{
	return PORTF_get_pin_level(2);
}

/**
 * \brief Set X5 pull mode
 *
 * Configure pin to pull up, down or disable pull mode, supported pull
 * modes are defined by device used
 *
 * \param[in] pull_mode Pin pull mode
 */
static inline void X5_set_pull_mode(const enum port_pull_mode pull_mode)
{
	PORTF_set_pin_pull_mode(3, pull_mode);
}

/**
 * \brief Set X5 data direction
 *
 * Select if the pin data direction is input, output or disabled.
 * If disabled state is not possible, this function throws an assert.
 *
 * \param[in] direction PORT_DIR_IN  = Data direction in
 *                      PORT_DIR_OUT = Data direction out
 *                      PORT_DIR_OFF = Disables the pin
 *                      (low power state)
 */
static inline void X5_set_dir(const enum port_dir dir)
{
	PORTF_set_pin_dir(3, dir);
}

/**
 * \brief Set X5 level
 *
 * Sets output level on a pin
 *
 * \param[in] level true  = Pin level set to "high" state
 *                  false = Pin level set to "low" state
 */
static inline void X5_set_level(const bool level)
{
	PORTF_set_pin_level(3, level);
}

/**
 * \brief Toggle output level on X5
 *
 * Toggle the pin level
 */
static inline void X5_toggle_level()
{
	PORTF_toggle_pin_level(3);
}

/**
 * \brief Get level on X5
 *
 * Reads the level on a pin
 */
static inline bool X5_get_level()
{
	return PORTF_get_pin_level(3);
}

/**
 * \brief Set X6 pull mode
 *
 * Configure pin to pull up, down or disable pull mode, supported pull
 * modes are defined by device used
 *
 * \param[in] pull_mode Pin pull mode
 */
static inline void X6_set_pull_mode(const enum port_pull_mode pull_mode)
{
	PORTF_set_pin_pull_mode(4, pull_mode);
}

/**
 * \brief Set X6 data direction
 *
 * Select if the pin data direction is input, output or disabled.
 * If disabled state is not possible, this function throws an assert.
 *
 * \param[in] direction PORT_DIR_IN  = Data direction in
 *                      PORT_DIR_OUT = Data direction out
 *                      PORT_DIR_OFF = Disables the pin
 *                      (low power state)
 */
static inline void X6_set_dir(const enum port_dir dir)
{
	PORTF_set_pin_dir(4, dir);
}

/**
 * \brief Set X6 level
 *
 * Sets output level on a pin
 *
 * \param[in] level true  = Pin level set to "high" state
 *                  false = Pin level set to "low" state
 */
static inline void X6_set_level(const bool level)
{
	PORTF_set_pin_level(4, level);
}

/**
 * \brief Toggle output level on X6
 *
 * Toggle the pin level
 */
static inline void X6_toggle_level()
{
	PORTF_toggle_pin_level(4);
}

/**
 * \brief Get level on X6
 *
 * Reads the level on a pin
 */
static inline bool X6_get_level()
{
	return PORTF_get_pin_level(4);
}

/**
 * \brief Set X7 pull mode
 *
 * Configure pin to pull up, down or disable pull mode, supported pull
 * modes are defined by device used
 *
 * \param[in] pull_mode Pin pull mode
 */
static inline void X7_set_pull_mode(const enum port_pull_mode pull_mode)
{
	PORTF_set_pin_pull_mode(5, pull_mode);
}

/**
 * \brief Set X7 data direction
 *
 * Select if the pin data direction is input, output or disabled.
 * If disabled state is not possible, this function throws an assert.
 *
 * \param[in] direction PORT_DIR_IN  = Data direction in
 *                      PORT_DIR_OUT = Data direction out
 *                      PORT_DIR_OFF = Disables the pin
 *                      (low power state)
 */
static inline void X7_set_dir(const enum port_dir dir)
{
	PORTF_set_pin_dir(5, dir);
}

/**
 * \brief Set X7 level
 *
 * Sets output level on a pin
 *
 * \param[in] level true  = Pin level set to "high" state
 *                  false = Pin level set to "low" state
 */
static inline void X7_set_level(const bool level)
{
	PORTF_set_pin_level(5, level);
}

/**
 * \brief Toggle output level on X7
 *
 * Toggle the pin level
 */
static inline void X7_toggle_level()
{
	PORTF_toggle_pin_level(5);
}

/**
 * \brief Get level on X7
 *
 * Reads the level on a pin
 */
static inline bool X7_get_level()
{
	return PORTF_get_pin_level(5);
}

#endif /* ATMEL_START_PINS_H_INCLUDED */
