metaneutrons/Amiga1200-Plus/Firmware/Keyboard/KeyboardController/KeyboardController/include/amigakb.h

/*
 * amigakb.h
 *
 * Created: 14/09/2019 19:32:03
 *  Author: jeroenvandezande
 */ 


#ifndef AMIGAKB_H_
#define AMIGAKB_H_


void amikb_sendkey(unsigned char keycode);
void amikb_init();


#endif /* AMIGAKB_H_ */
