metaneutrons/Amiga1200-Plus/Firmware/Keyboard/KeyboardController/KeyboardController/src/key_scan.c

/*
* key_scan.c
*
* Created: 14/09/2019 16:03:36
*  Author: Jeroen Vandezande
*/
#include <port.h>
#include <atmel_start.h>
#include <util/delay.h>


void (*XDDRArray[6]) (const enum port_dir dir);
bool (*YInputArray[15]) ();

//see http://amigadev.elowar.com/read/ADCD_2.1/Hardware_Manual_guide/node017A.html
const uint8_t keycodes[6][15] =
{
	{0x5F, 0x59, 0x58, 0x57, 0x56, 0x5C, 0x55, 0x5B, 0x54, 0x53, 0x52, 0x51, 0x50, 0x5A, 0x45},
	{0x4C, 0x0D, 0x0C, 0x0B, 0x0A, 0x09, 0x08, 0x07, 0x06, 0x05, 0x04, 0x03, 0x02, 0x01, 0x00},
	{0x4F, 0x44, 0x1B, 0x1A, 0x19, 0x18, 0x17, 0x16, 0x15, 0x14, 0X13, 0x12, 0x11, 0x10, 0x42},
	{0x4E, 0x46, 0x2B, 0x2A, 0x29, 0x28, 0x27, 0x26, 0x25, 0X24, 0x23, 0x22, 0x21, 0x20, 0x62},
	{0x4D, 0x41, 0x40, 0x3B, 0x3A, 0x39, 0x38, 0x37, 0x36, 0x35, 0X34, 0x33, 0x32, 0x31, 0x30},
	{0x4A, 0x0F, 0x1D, 0x2D, 0x3D, 0x43, 0x1E, 0x2E, 0x3E, 0x3C, 0x1F, 0x2F, 0x3F, 0x5E, 0x5D}
};

bool prevkeystates[6][15];
bool prevLeftAmiga = false;
bool prevLeftAlt = false;
bool prevLeftShift = false;
bool prevCTRL = false;
bool prevRightAmiga = false;
bool prevRightAlt = false;
bool prevRightShift = false;
int currentX;

bool getResetState()
{
  return !prevLeftAmiga && !prevRightAmiga && !prevCTRL;
}

void keyscan_init()
{
	XDDRArray[0] = X2_set_dir;
	XDDRArray[1] = X3_set_dir;
	XDDRArray[2] = X4_set_dir;
	XDDRArray[3] = X5_set_dir;
	XDDRArray[4] = X6_set_dir;
	XDDRArray[5] = X7_set_dir;
	
	YInputArray[0] = Y0_get_level;
	YInputArray[1] = Y1_get_level;
	YInputArray[2] = Y2_get_level;
	YInputArray[3] = Y3_get_level;
	YInputArray[4] = Y4_get_level;
	YInputArray[5] = Y5_get_level;
	YInputArray[6] = Y6_get_level;
	YInputArray[7] = Y7_get_level;
	YInputArray[8] = Y8_get_level;
	YInputArray[9] = Y9_get_level;
	YInputArray[10] = Y10_get_level;
	YInputArray[11] = Y11_get_level;
	YInputArray[12] = Y12_get_level;
	YInputArray[13] = Y13_get_level;
	YInputArray[14] = Y14_get_level;

	for (int x = 0; x < 6; x++)
	{
		for (int y = 0; y < 15; y++)
		{
			prevkeystates[x][y] = false;
		}
	}
	currentX = 0;
}

int scankeys()
{

  //while(1)
  //{
    //X2_set_dir(PORT_DIR_OUT);
	//X3_set_dir(PORT_DIR_OUT);
	//X4_set_dir(PORT_DIR_OUT);
	//X5_set_dir(PORT_DIR_OUT);
	//X6_set_level(false);
	//X6_set_dir(PORT_DIR_OUT);
	//X7_set_dir(PORT_DIR_OUT);
	//PORTF = 0;
	//DDRF = 255;
	//CapsLockLed_set_level(Y1_get_level());
  //}
   
	while (1)
	{
		XDDRArray[currentX](PORT_DIR_IN);
		currentX++;
		if (currentX > 5) currentX = 0;
		XDDRArray[currentX](PORT_DIR_OUT);
		_delay_us(600);
		for (int y = 0; y < 15; y++)
		{
			bool temp = !YInputArray[y]();
			if (temp != prevkeystates[currentX][y])
			{

				prevkeystates[currentX][y] = temp;
				uint8_t tempscancode = keycodes[currentX][y];
				//uint8_t tempscancode = 0x36;
				if (temp) 
				{
					tempscancode |= 0x80; //set bit 7 to one , indicating key pressed
				}
				return tempscancode;
			}

			//(Bit 6) (Bit 5) (Bit 4) (Bit 3) (Bit 2) (Bit 1) (Bit 0)
			//+-------+-------+-------+-------+-------+-------+-------+
			//| LEFT  | LEFT  | LEFT  | CTRL  | RIGHT | RIGHT | RIGHT |
			//| AMIGA | ALT   | SHIFT |       | AMIGA |  ALT  | SHIFT |
			//| (66)  | (64)  | (60)  | (63)  | (67)  | (65)  | (61)  |
			//+-------+-------+-------+-------+-------+-------+-------+

		}
		if(LAMI_get_level() != prevLeftAmiga)
		{
			prevLeftAmiga = LAMI_get_level();
			return (!prevLeftAmiga ? 0x66 | 0x80 : 0x66);
		}
		if(RAMI_get_level() != prevRightAmiga)
		{
			prevRightAmiga = RAMI_get_level();
			return (!prevRightAmiga ? 0x67 | 0x80 : 0x67);
		}
		if(LALT_get_level() != prevLeftAlt)
		{
			prevLeftAlt = LALT_get_level();
			return (!prevLeftAlt ? 0x64 | 0x80 : 0x64);
		}
		if(LSHF_get_level() != prevLeftShift)
		{
			prevLeftShift = LSHF_get_level();
			return (!prevLeftShift ? 0x60 | 0x80 : 0x60);
		}
		if(CTRL_get_level() != prevCTRL)
		{
			prevCTRL = CTRL_get_level();
			return (!prevCTRL ? 0x63 | 0x80 : 0x63);
		}
		if(RALT_get_level() != prevRightAlt)
		{
			prevRightAlt = CTRL_get_level();
			return (!prevRightAlt ? 0x65 | 0x80 : 0x65);
		}
		if(RSHF_get_level() != prevRightShift)
		{
			prevRightShift = RSHF_get_level();
			return (!prevRightShift ? 0x61 | 0x80 : 0x61);
		}
	}
}
